ManuFerHi/ZXUNO_VGA_2M/Pics/IMG_20170301_200429.jpg

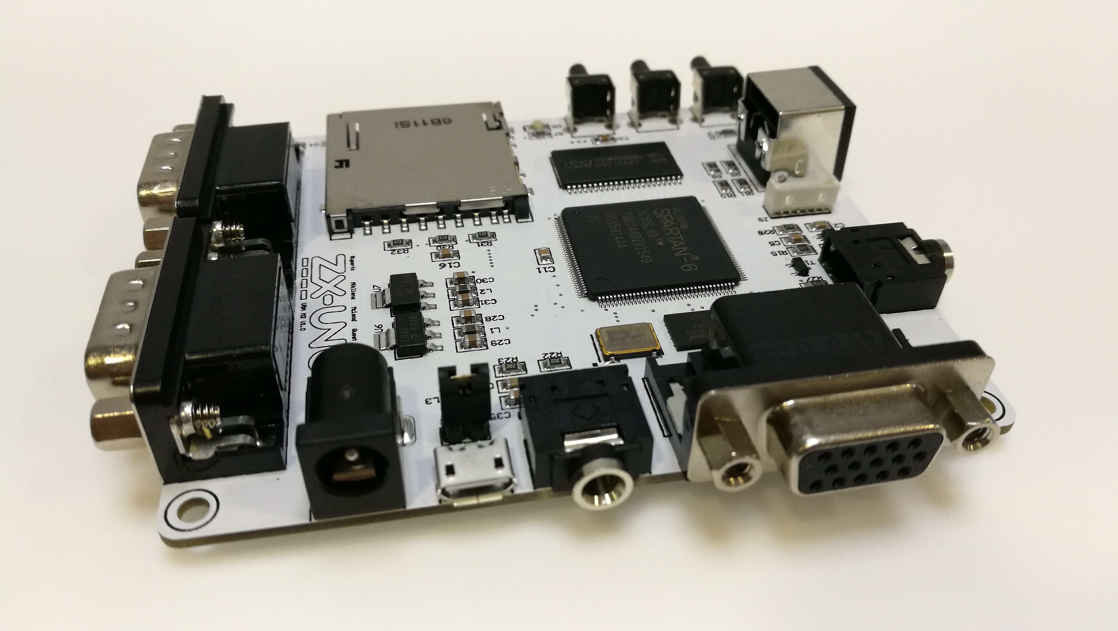
Pics/IMG_20170301_200429.jpg
