ManuFerHi/ZXUNO_VGA_2M/Pics/IMG_20170307_123520.jpg

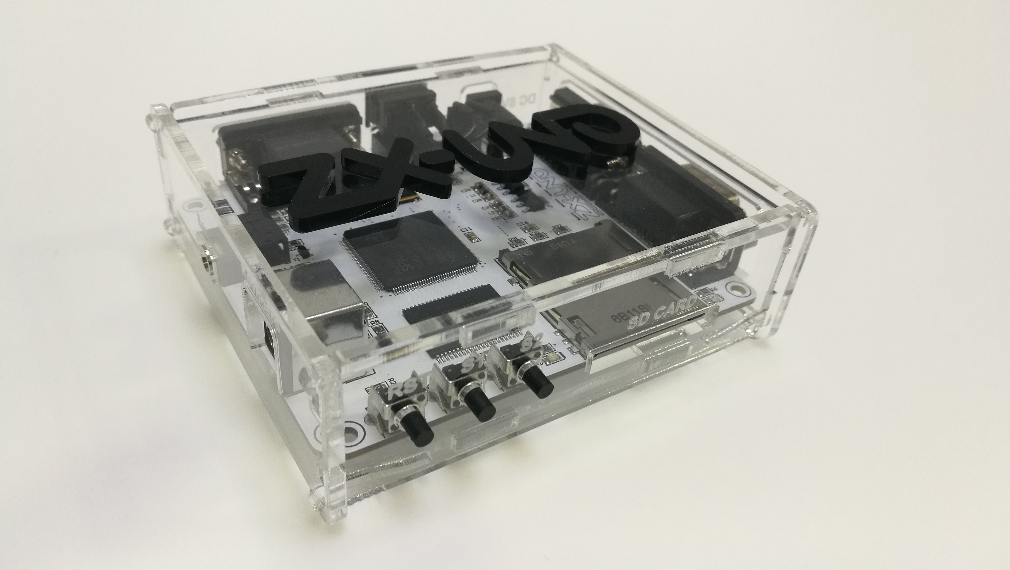
Pics/IMG_20170307_123520.jpg
