ManuFerHi/ZXUNO_VGA_2M/Pics/IMG_20170307_123532.jpg

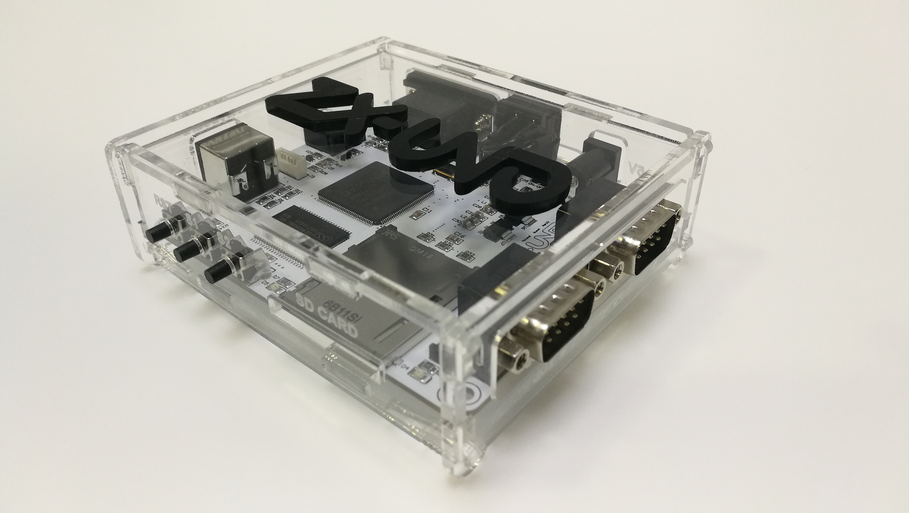
Pics/IMG_20170307_123532.jpg
