ManuFerHi/ZXUNO_VGA_2M/Pics/IMG_20170307_124048.jpg

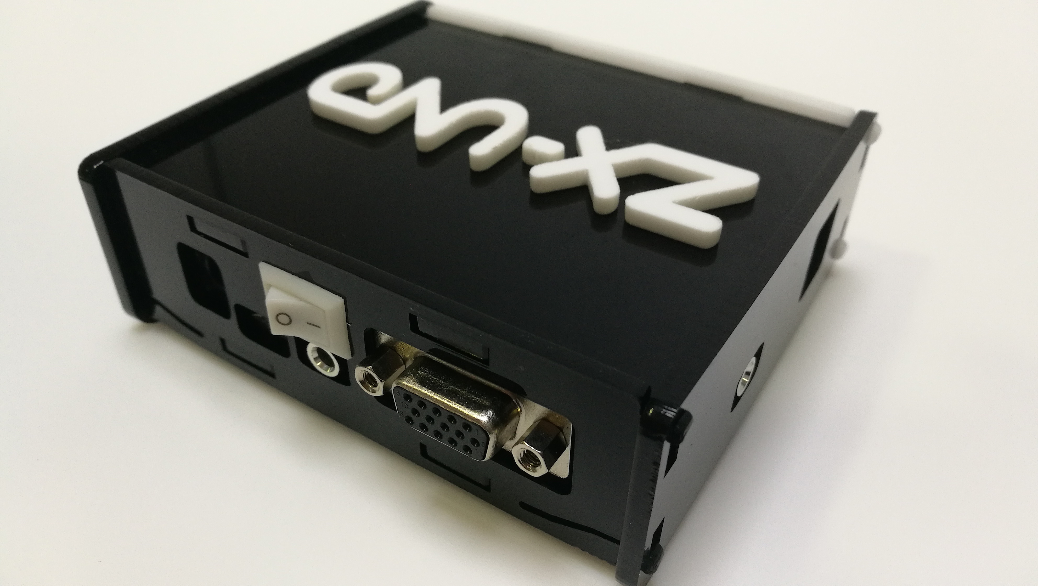
Pics/IMG_20170307_124048.jpg
